Egyras/HeishaMon/HeishaMon/src/opentherm/opentherm.cpp

/*
  OpenTherm.cpp - OpenTherm Communication Library For Arduino, ESP8266
  Copyright 2018, Ihor Melnyk
*/

#include "opentherm.h"

OpenTherm::OpenTherm(int inPin, int outPin, bool isSlave)
  : status(OpenThermStatus::NOT_INITIALIZED),
    inPin(inPin),
    outPin(outPin),
    isSlave(isSlave),
    response(0),
    responseStatus(OpenThermResponseStatus::NONE),
    responseTimestamp(0),
    handleInterruptCallback(NULL),
    processResponseCallback(NULL) {
}

void OpenTherm::begin(void (*handleInterruptCallback)(void), void (*processResponseCallback)(unsigned long, OpenThermResponseStatus)) {
  pinMode(inPin, INPUT);
  pinMode(outPin, OUTPUT);
  if (handleInterruptCallback != NULL) {
    this->handleInterruptCallback = handleInterruptCallback;
    attachInterrupt(digitalPinToInterrupt(inPin), handleInterruptCallback, CHANGE);
  }
  activateBoiler();
  status = OpenThermStatus::READY;
  this->processResponseCallback = processResponseCallback;
}

void OpenTherm::begin(void (*handleInterruptCallback)(void)) {
  begin(handleInterruptCallback, NULL);
}

bool IRAM_ATTR OpenTherm::isReady() {
  return status == OpenThermStatus::READY;
}

int IRAM_ATTR OpenTherm::readState() {
  return digitalRead(inPin);
}

void OpenTherm::setActiveState() {
  digitalWrite(outPin, !logicalSendHigh);
}

void OpenTherm::setIdleState() {
  digitalWrite(outPin, logicalSendHigh);
}

void OpenTherm::activateBoiler() {
  setIdleState();
  delay(1000);
}

void OpenTherm::sendBit(bool high) {
  if (high) setActiveState();
  else setIdleState();
  delayMicroseconds(500);
  if (high) setIdleState();
  else setActiveState();
  delayMicroseconds(500);
}

bool OpenTherm::sendRequestAync(unsigned long request) {
  //Serial.println("Request: " + String(request, HEX));
  noInterrupts();
  const bool ready = isReady();
  interrupts();

  if (!ready)
    return false;

  status = OpenThermStatus::REQUEST_SENDING;
  response = 0;
  responseStatus = OpenThermResponseStatus::NONE;

  sendBit(HIGH);  //start bit
  for (int i = 31; i >= 0; i--) {
    sendBit(bitRead(request, i));
  }
  sendBit(HIGH);  //stop bit
  setIdleState();

  status = OpenThermStatus::RECEIVE_WAITING;
  responseTimestamp = micros();
  return true;
}

unsigned long OpenTherm::sendRequest(unsigned long request) {
  if (!sendRequestAync(request)) return 0;
  while (!isReady()) {
    process();
    yield();
  }
  return response;
}

bool OpenTherm::sendResponse(unsigned long request) {
  status = OpenThermStatus::REQUEST_SENDING;
  response = 0;
  responseStatus = OpenThermResponseStatus::NONE;

  sendBit(HIGH);  //start bit
  for (int i = 31; i >= 0; i--) {
    sendBit(bitRead(request, i));
  }
  sendBit(HIGH);  //stop bit
  setIdleState();
  status = OpenThermStatus::READY;
  return true;
}

OpenThermResponseStatus OpenTherm::getLastResponseStatus() {
  return responseStatus;
}

void IRAM_ATTR OpenTherm::handleInterrupt() {
  unsigned long newTs = micros();

  if (isSlave && smartPowerEnabled) {
    if ((status == OpenThermStatus::READY) && (smartPowerState == HIGH_POWER) && ((newTs - responseTimestamp) > 9000) && ((newTs - responseTimestamp) < 11000)) {
      //previous transit was from LOW to MEDIUM (via HIGH)
      logicalReceiveHigh = !logicalReceiveHigh;
      status = OpenThermStatus::READY;
      smartPowerState = MEDIUM_POWER;
      return;
    }
    if ((status == OpenThermStatus::RECEIVE_START_BIT) && (smartPowerState == MEDIUM_POWER) && ((newTs - responseTimestamp) > 15000)) {
      //this is a MEDIUM to LOW request
      logicalSendHigh = !logicalSendHigh;
      setIdleState();
      status = OpenThermStatus::READY;
      smartPowerState = LOW_POWER;
      return;
    }
  }

  if (isReady()) {
    if (isSlave && readState() == logicalReceiveHigh) {
      status = OpenThermStatus::RECEIVE_WAITING;
    } else {
      return;
    }
  }


  if (status == OpenThermStatus::RECEIVE_WAITING) {
    if (readState() == logicalReceiveHigh) {
      status = OpenThermStatus::RECEIVE_START_BIT;
      responseTimestamp = newTs;
    } else {
      status = OpenThermStatus::RECEIVE_INVALID;
      responseTimestamp = newTs;
    }
  } else if (status == OpenThermStatus::RECEIVE_START_BIT) {
    if ((newTs - responseTimestamp < 750) && readState() == !logicalReceiveHigh) {
      status = OpenThermStatus::RECEIVE_DATA;
      responseTimestamp = newTs;
      responseBitIndex = 0;
    } else {
      status = OpenThermStatus::RECEIVE_INVALID;
      responseTimestamp = newTs;
    }
  } else if (status == OpenThermStatus::RECEIVE_DATA) {
    if ((newTs - responseTimestamp) > 750) {
      if (responseBitIndex < 32) {
        response = (response << 1) | !(readState() == logicalReceiveHigh);
        responseTimestamp = newTs;
        responseBitIndex++;
      } else {  //stop bit
        status = OpenThermStatus::RECEIVE_READY;
        responseTimestamp = newTs;
      }
    }
  }
}

void OpenTherm::process() {
  noInterrupts();
  OpenThermStatus st = status;
  unsigned long ts = responseTimestamp;
  interrupts();

  unsigned long newTs = micros();

  if (st == OpenThermStatus::RECEIVE_START_BIT && (readState() == LOW) && ((newTs - ts) > 5000000)) {  //short circuit detected, act as on/off
    //Serial.println("Short circuit, switch to on/off");
    status = OpenThermStatus::ON_OFF;
    return;
  } else if (st == OpenThermStatus::ON_OFF) {
    if (readState() == HIGH) {
      //Serial.println("Short circuit removed, switch to opentherm");
      status = OpenThermStatus::NOT_INITIALIZED;
      return;
    } else {
      //Serial.println("Still in on/off, short circuit active.");
      return;
    }
  }

  if (isSlave && smartPowerEnabled && smartPowerState != LOW_POWER && (newTs - ts) > 1150000) {  //timeout for 1 + 15% second. thermostat disconnected? disable smartpower
    logicalReceiveHigh = HIGH;
    logicalSendHigh = HIGH;
    setIdleState();
    smartPowerState = LOW_POWER;
    smartPowerEnabled = false;
    OpenThermStatus::NOT_INITIALIZED;
  }

  if (st == OpenThermStatus::READY) return;

  if (st != OpenThermStatus::NOT_INITIALIZED && (newTs - ts) > 1000000) {
    status = OpenThermStatus::READY;
    responseStatus = OpenThermResponseStatus::TIMEOUT;
    if (processResponseCallback != NULL) {
      processResponseCallback(response, responseStatus);
    }
  } else if (st == OpenThermStatus::RECEIVE_INVALID) {
    status = OpenThermStatus::DELAY;
    responseStatus = OpenThermResponseStatus::INVALID;
    if (processResponseCallback != NULL) {
      processResponseCallback(response, responseStatus);
    }
  } else if (st == OpenThermStatus::RECEIVE_READY) {
    status = OpenThermStatus::DELAY;
    responseStatus = (isSlave ? isValidRequest(response) : isValidResponse(response)) ? OpenThermResponseStatus::SUCCESS : OpenThermResponseStatus::INVALID;
    if (processResponseCallback != NULL) {
      processResponseCallback(response, responseStatus);
    }
  } else if (st == OpenThermStatus::DELAY) {
    if ((newTs - ts) > 100000) {
      status = OpenThermStatus::READY;
    }
  } else if (isSlave && smartPowerEnabled && (st == OpenThermStatus::RECEIVE_START_BIT) && ((newTs - ts) > 5000)) {
    if (smartPowerState == LOW_POWER) {  // currently in normal mode
      logicalSendHigh = !logicalSendHigh;
      logicalReceiveHigh = !logicalReceiveHigh;
      setIdleState();
      status = OpenThermStatus::READY;
      smartPowerState = HIGH_POWER;
    } else if (smartPowerState == HIGH_POWER) {  //switch from HIGH to LOW
      logicalReceiveHigh = !logicalReceiveHigh;
      logicalSendHigh = !logicalSendHigh;
      setIdleState();
      status = OpenThermStatus::READY;
      smartPowerState = LOW_POWER;
    }
  }
}

bool OpenTherm::parity(unsigned long frame)  //odd parity
{
  byte p = 0;
  while (frame > 0) {
    if (frame & 1) p++;
    frame = frame >> 1;
  }
  return (p & 1);
}

OpenThermMessageType OpenTherm::getMessageType(unsigned long message) {
  OpenThermMessageType msg_type = static_cast<OpenThermMessageType>((message >> 28) & 7);
  return msg_type;
}

OpenThermMessageID OpenTherm::getDataID(unsigned long frame) {
  return (OpenThermMessageID)((frame >> 16) & 0xFF);
}

unsigned long OpenTherm::buildRequest(OpenThermMessageType type, OpenThermMessageID id, unsigned int data) {
  unsigned long request = data;
  if (type == OpenThermMessageType::WRITE_DATA) {
    request |= 1ul << 28;
  }
  request |= ((unsigned long)id) << 16;
  if (parity(request)) request |= (1ul << 31);
  return request;
}

unsigned long OpenTherm::buildResponse(OpenThermMessageType type, OpenThermMessageID id, unsigned int data) {
  unsigned long response = data;
  response |= type << 28;
  response |= ((unsigned long)id) << 16;
  if (parity(response)) response |= (1ul << 31);
  return response;
}

bool OpenTherm::isValidResponse(unsigned long response) {
  if (parity(response)) return false;
  byte msgType = (response << 1) >> 29;
  return msgType == READ_ACK || msgType == WRITE_ACK;
}

bool OpenTherm::isValidRequest(unsigned long request) {
  if (parity(request)) return false;
  byte msgType = (request << 1) >> 29;
  return msgType == READ_DATA || msgType == WRITE_DATA;
}

void OpenTherm::end() {
  if (this->handleInterruptCallback != NULL) {
    detachInterrupt(digitalPinToInterrupt(inPin));
  }
}
/*
const char *OpenTherm::statusToString(OpenThermResponseStatus status) {
  switch (status) {
    case NONE: return "NONE";
    case SUCCESS: return "SUCCESS";
    case INVALID: return "INVALID";
    case TIMEOUT: return "TIMEOUT";
    default: return "UNKNOWN";
  }
}

const char *OpenTherm::messageTypeToString(OpenThermMessageType message_type) {
  switch (message_type) {
    case READ_DATA: return "READ_DATA";
    case WRITE_DATA: return "WRITE_DATA";
    case INVALID_DATA: return "INVALID_DATA";
    case RESERVED: return "RESERVED";
    case READ_ACK: return "READ_ACK";
    case WRITE_ACK: return "WRITE_ACK";
    case DATA_INVALID: return "DATA_INVALID";
    case UNKNOWN_DATA_ID: return "UNKNOWN_DATA_ID";
    default: return "UNKNOWN";
  }
}
*/

//building requests

unsigned long OpenTherm::buildSetBoilerStatusRequest(bool enableCentralHeating, bool enableHotWater, bool enableCooling, bool enableOutsideTemperatureCompensation, bool enableCentralHeating2) {
  unsigned int data = enableCentralHeating | (enableHotWater << 1) | (enableCooling << 2) | (enableOutsideTemperatureCompensation << 3) | (enableCentralHeating2 << 4);
  data <<= 8;
  return buildRequest(OpenThermMessageType::READ_DATA, OpenThermMessageID::Status, data);
}

unsigned long OpenTherm::buildSetBoilerTemperatureRequest(float temperature) {
  unsigned int data = temperatureToData(temperature);
  return buildRequest(OpenThermMessageType::WRITE_DATA, OpenThermMessageID::TSet, data);
}

unsigned long OpenTherm::buildGetBoilerTemperatureRequest() {
  return buildRequest(OpenThermMessageType::READ_DATA, OpenThermMessageID::Tboiler, 0);
}

//parsing responses
bool OpenTherm::isFault(unsigned long response) {
  return response & 0x1;
}

bool OpenTherm::isCentralHeatingActive(unsigned long response) {
  return response & 0x2;
}

bool OpenTherm::isHotWaterActive(unsigned long response) {
  return response & 0x4;
}

bool OpenTherm::isFlameOn(unsigned long response) {
  return response & 0x8;
}

bool OpenTherm::isCoolingActive(unsigned long response) {
  return response & 0x10;
}

bool OpenTherm::isDiagnostic(unsigned long response) {
  return response & 0x40;
}

uint16_t OpenTherm::getUInt(const unsigned long response) const {
  const uint16_t u88 = response & 0xffff;
  return u88;
}

float OpenTherm::getFloat(const unsigned long response) const {
  const uint16_t u88 = getUInt(response);
  const float f = (u88 & 0x8000) ? -(0x10000L - u88) / 256.0f : u88 / 256.0f;
  return f;
}

unsigned int OpenTherm::temperatureToData(float temperature) {
  if (temperature < 0) temperature = 0;
  if (temperature > 100) temperature = 100;
  unsigned int data = (unsigned int)(temperature * 256);
  return data;
}

//basic requests

unsigned long OpenTherm::setBoilerStatus(bool enableCentralHeating, bool enableHotWater, bool enableCooling, bool enableOutsideTemperatureCompensation, bool enableCentralHeating2) {
  return sendRequest(buildSetBoilerStatusRequest(enableCentralHeating, enableHotWater, enableCooling, enableOutsideTemperatureCompensation, enableCentralHeating2));
}

bool OpenTherm::setBoilerTemperature(float temperature) {
  unsigned long response = sendRequest(buildSetBoilerTemperatureRequest(temperature));
  return isValidResponse(response);
}

float OpenTherm::getBoilerTemperature() {
  unsigned long response = sendRequest(buildGetBoilerTemperatureRequest());
  return isValidResponse(response) ? getFloat(response) : 0;
}

float OpenTherm::getReturnTemperature() {
  unsigned long response = sendRequest(buildRequest(OpenThermRequestType::READ, OpenThermMessageID::Tret, 0));
  return isValidResponse(response) ? getFloat(response) : 0;
}

bool OpenTherm::setDHWSetpoint(float temperature) {
  unsigned int data = temperatureToData(temperature);
  unsigned long response = sendRequest(buildRequest(OpenThermMessageType::WRITE_DATA, OpenThermMessageID::TdhwSet, data));
  return isValidResponse(response);
}

float OpenTherm::getDHWTemperature() {
  unsigned long response = sendRequest(buildRequest(OpenThermMessageType::READ_DATA, OpenThermMessageID::Tdhw, 0));
  return isValidResponse(response) ? getFloat(response) : 0;
}

float OpenTherm::getModulation() {
  unsigned long response = sendRequest(buildRequest(OpenThermRequestType::READ, OpenThermMessageID::RelModLevel, 0));
  return isValidResponse(response) ? getFloat(response) : 0;
}

float OpenTherm::getPressure() {
  unsigned long response = sendRequest(buildRequest(OpenThermRequestType::READ, OpenThermMessageID::CHPressure, 0));
  return isValidResponse(response) ? getFloat(response) : 0;
}

unsigned char OpenTherm::getFault() {
  return ((sendRequest(buildRequest(OpenThermRequestType::READ, OpenThermMessageID::ASFflags, 0)) >> 8) & 0xff);
}

void OpenTherm::setSmartPower(bool state) {
  smartPowerEnabled = state;
  smartPowerState = LOW_POWER;  //check later if this is the right location, maybe in begin
}
