Egyras/HeishaMon/HeishaMon/commands.h

#define LWIP_INTERNAL

#include <ArduinoJson.h>

#define DATASIZE 203

#define INITIALQUERYSIZE 7
extern byte initialQuery[INITIALQUERYSIZE];
#define PANASONICQUERYSIZE 110
extern byte panasonicQuery[PANASONICQUERYSIZE];


#define OPTDATASIZE 20
#define OPTIONALPCBQUERYTIME 1000 //send optional pcb query each second
#define OPTIONALPCBQUERYSIZE 19
#define OPTIONALPCBSAVETIME 300 //save each 5 minutes the current optional pcb state into flash to have valid values during reboot
extern byte optionalPCBQuery[OPTIONALPCBQUERYSIZE];


extern const char* mqtt_topic_values;
extern const char* mqtt_topic_xvalues;
extern const char* mqtt_topic_commands;
extern const char* mqtt_topic_pcbvalues;
extern const char* mqtt_topic_1wire;
extern const char* mqtt_topic_s0;
extern const char* mqtt_topic_pcb;
extern const char* mqtt_logtopic;
extern const char* mqtt_willtopic;
extern const char* mqtt_iptopic;
extern const char* mqtt_send_raw_value_topic;

unsigned int set_heatpump_state(char *msg, unsigned char *cmd, char *log_msg);
unsigned int set_pump(char *msg, unsigned char *cmd, char *log_msg);
unsigned int set_max_pump_duty(char *msg, unsigned char *cmd, char *log_msg);
unsigned int set_quiet_mode(char *msg, unsigned char *cmd, char *log_msg);
unsigned int set_z1_heat_request_temperature(char *msg, unsigned char *cmd, char *log_msg);
unsigned int set_z1_cool_request_temperature(char *msg, unsigned char *cmd, char *log_msg);
unsigned int set_z2_heat_request_temperature(char *msg, unsigned char *cmd, char *log_msg);
unsigned int set_z2_cool_request_temperature(char *msg, unsigned char *cmd, char *log_msg);
unsigned int set_force_DHW(char *msg, unsigned char *cmd, char *log_msg);
unsigned int set_force_defrost(char *msg, unsigned char *cmd, char *log_msg);
unsigned int set_force_sterilization(char *msg, unsigned char *cmd, char *log_msg);
unsigned int set_holiday_mode(char *msg, unsigned char *cmd, char *log_msg);
unsigned int set_powerful_mode(char *msg, unsigned char *cmd, char *log_msg);
unsigned int set_operation_mode(char *msg, unsigned char *cmd, char *log_msg);
unsigned int set_DHW_temp(char *msg, unsigned char *cmd, char *log_msg);
unsigned int set_curves(char *msg, unsigned char *cmd, char *log_msg);
unsigned int set_zones(char *msg, unsigned char *cmd, char *log_msg);
unsigned int set_floor_heat_delta(char *msg, unsigned char *cmd, char *log_msg);
unsigned int set_floor_cool_delta(char *msg, unsigned char *cmd, char *log_msg);
unsigned int set_dhw_heat_delta(char *msg, unsigned char *cmd, char *log_msg);
unsigned int set_reset(char *msg, unsigned char *cmd, char *log_msg);
unsigned int set_heater_delay_time(char *msg, unsigned char *cmd, char *log_msg);
unsigned int set_heater_start_delta(char *msg, unsigned char *cmd, char *log_msg);
unsigned int set_heater_stop_delta(char *msg, unsigned char *cmd, char *log_msg);
unsigned int set_main_schedule(char *msg, unsigned char *cmd, char *log_msg);
unsigned int set_alt_external_sensor(char *msg, unsigned char *cmd, char *log_msg);
unsigned int set_external_pad_heater(char *msg, unsigned char *cmd, char *log_msg);
unsigned int set_buffer_delta(char *msg, unsigned char *cmd, char *log_msg);
unsigned int set_buffer(char *msg, unsigned char *cmd, char *log_msg);
unsigned int set_heatingoffoutdoortemp(char *msg, unsigned char *cmd, char *log_msg);
unsigned int set_bivalent_control(char *msg, unsigned char *cmd, char *log_msg);
unsigned int set_bivalent_mode(char *msg, unsigned char *cmd, char *log_msg);
unsigned int set_bivalent_start_temp(char *msg, unsigned char *cmd, char *log_msg);
unsigned int set_bivalent_ap_start_temp(char *msg, unsigned char *cmd, char *log_msg);
unsigned int set_bivalent_ap_stop_temp(char *msg, unsigned char *cmd, char *log_msg);
unsigned int set_external_control(char *msg, unsigned char *cmd, char *log_msg);
unsigned int set_external_error(char *msg, unsigned char *cmd, char *log_msg);
unsigned int set_heatingcontrol(char *msg, unsigned char *cmd, char *log_msg);
unsigned int set_smart_dhw(char *msg, unsigned char *cmd, char *log_msg);
unsigned int set_quiet_mode_priority(char *msg, unsigned char *cmd, char *log_msg);
unsigned int set_pump_flowrate_mode(char *msg, unsigned char *cmd, char *log_msg);


//optional pcb commands
unsigned int set_heat_cool_mode(char *msg, char *log_msg);
unsigned int set_compressor_state(char *msg, char *log_msg);
unsigned int set_smart_grid_mode(char *msg, char *log_msg);
unsigned int set_external_thermostat_1_state(char *msg, char *log_msg);
unsigned int set_external_thermostat_2_state(char *msg, char *log_msg);
unsigned int set_demand_control(char *msg, char *log_msg);
unsigned int set_pool_temp(char *msg, char *log_msg);
unsigned int set_buffer_temp(char *msg, char *log_msg);
unsigned int set_z1_room_temp(char *msg, char *log_msg);
unsigned int set_z1_water_temp(char *msg, char *log_msg);
unsigned int set_z2_room_temp(char *msg, char *log_msg);
unsigned int set_z2_water_temp(char *msg, char *log_msg);
unsigned int set_solar_temp(char *msg, char *log_msg);
unsigned int set_byte_9(char *msg, char *log_msg);
unsigned int set_external_compressor_control(char *msg, unsigned char *cmd, char *log_msg);
unsigned int set_external_heat_cool_control(char *msg, unsigned char *cmd, char *log_msg);

struct cmdStruct {
  char name[29];
  unsigned int (*func)(char *msg, unsigned char *cmd, char *log_msg);
};

const cmdStruct commands[] PROGMEM = {
  // set heatpump state to on by sending 1
  { "SetHeatpump", set_heatpump_state },
  // set pump state to on by sending 1
  { "SetPump", set_pump },
  // set max pump duty
  { "SetMaxPumpDuty", set_max_pump_duty },
  // set 0 for Off mode, set 1 for Quiet mode 1, set 2 for Quiet mode 2, set 3 for Quiet mode 3
  { "SetQuietMode", set_quiet_mode },
  // z1 heat request temp -  set from -5 to 5 to get same temperature shift point or set direct temp
  { "SetZ1HeatRequestTemperature", set_z1_heat_request_temperature },
  // z1 cool request temp -  set from -5 to 5 to get same temperature shift point or set direct temp
  { "SetZ1CoolRequestTemperature", set_z1_cool_request_temperature },
  // z2 heat request temp -  set from -5 to 5 to get same temperature shift point or set direct temp
  { "SetZ2HeatRequestTemperature", set_z2_heat_request_temperature },
  // z2 cool request temp -  set from -5 to 5 to get same temperature shift point or set direct temp
  { "SetZ2CoolRequestTemperature", set_z2_cool_request_temperature },
  // set mode to force DHW by sending 1
  { "SetForceDHW", set_force_DHW },
  // set mode to force defrost  by sending 1
  { "SetForceDefrost", set_force_defrost },
  // set mode to force sterilization by sending 1
  { "SetForceSterilization", set_force_sterilization },
  // set Holiday mode by sending 1, off will be 0
  { "SetHolidayMode", set_holiday_mode },
  // set Powerful mode by sending 0 = off, 1 for 30min, 2 for 60min, 3 for 90 min
  { "SetPowerfulMode", set_powerful_mode },
  // set Heat pump operation mode  3 = DHW only, 0 = heat only, 1 = cool only, 2 = Auto, 4 = Heat+DHW, 5 = Cool+DHW, 6 = Auto + DHW
  { "SetOperationMode", set_operation_mode },
  // set DHW temperature by sending desired temperature between 40C-75C
  { "SetDHWTemp", set_DHW_temp },
  // set heat/cool curves on z1 and z2 using a json input
  { "SetCurves", set_curves },
  // set zones to active
  { "SetZones", set_zones },
  { "SetFloorHeatDelta", set_floor_heat_delta },
  { "SetFloorCoolDelta", set_floor_cool_delta },
  { "SetDHWHeatDelta", set_dhw_heat_delta },
  { "SetReset", set_reset },
  { "SetHeaterDelayTime", set_heater_delay_time },
  { "SetHeaterStartDelta", set_heater_start_delta },
  { "SetHeaterStopDelta", set_heater_stop_delta },
  { "SetMainSchedule", set_main_schedule },
  { "SetAltExternalSensor", set_alt_external_sensor },
  { "SetExternalPadHeater", set_external_pad_heater },
  { "SetBufferDelta", set_buffer_delta },
  { "SetBuffer", set_buffer },
  // set Outdoor Temperature to stop heating 5-35
  { "SetHeatingOffOutdoorTemp", set_heatingoffoutdoortemp },
  { "SetExternalControl", set_external_control },
  { "SetExternalError", set_external_error },
  { "SetExternalCompressorControl", set_external_compressor_control },
  { "SetExternalHeatCoolControl", set_external_heat_cool_control },
  // set Bivalent control mode  0 = off, 1 = on
  { "SetBivalentControl", set_bivalent_control },
  // set Bivalent operation mode  0 = Alternativ, 1 = Parallel, 2 = Advanced Parallel
  { "SetBivalentMode", set_bivalent_mode },
  // bivalent start temp -  set from -15C to 35C 
  { "SetBivalentStartTemp", set_bivalent_start_temp },
  // bivalent AP start temp -  set from -15C to 35C 
  { "SetBivalentAPStartTemp", set_bivalent_ap_start_temp },
  // bivalent AP stop temp -  set from -15C to 35C
  { "SetBivalentAPStopTemp", set_bivalent_ap_stop_temp },
  { "SetHeatingControl", set_heatingcontrol },
  { "SetSmartDHW", set_smart_dhw },
  { "SetQuietModePriority", set_quiet_mode_priority },
  { "SetPumpFlowrateMode", set_pump_flowrate_mode },
};

struct optCmdStruct{
  char name[28];
  unsigned int (*func)(char *msg, char *log_msg);
};

const optCmdStruct optionalCommands[] PROGMEM = {
  // optional PCB
  { "SetHeatCoolMode", set_heat_cool_mode },
  { "SetCompressorState", set_compressor_state },
  { "SetSmartGridMode", set_smart_grid_mode },
  { "SetExternalThermostat1State", set_external_thermostat_1_state },
  { "SetExternalThermostat2State", set_external_thermostat_2_state },
  { "SetDemandControl", set_demand_control },
  { "SetPoolTemp", set_pool_temp },
  { "SetBufferTemp", set_buffer_temp },
  { "SetZ1RoomTemp", set_z1_room_temp },
  { "SetZ1WaterTemp", set_z1_water_temp },
  { "SetZ2RoomTemp", set_z2_room_temp },
  { "SetZ2WaterTemp", set_z2_water_temp },
  { "SetSolarTemp", set_solar_temp },
  { "SetOptPCBByte9", set_byte_9 }
};

void send_heatpump_command(char* topic, char *msg, bool (*send_command)(byte*, int), void (*log_message)(char*), bool optionalPCB);
bool saveOptionalPCB(byte* command, int length);
bool loadOptionalPCB(byte* command, int length);
