Egyras/HeishaMon/HeishaMon/decode.cpp

#include "decode.h"
#include "commands.h"
#include "rules.h"
#include "src/common/progmem.h"

void websocket_write_all(char *data, uint16_t data_len);

unsigned long lastalldatatime = 0;
unsigned long lastallextradatatime = 0;
unsigned long lastalloptdatatime = 0;

String getBit1(byte input) {
  return String(input  >> 7);
}

String getBit1and2(byte input) {
  return String((input  >> 6) - 1);
}

String getBit3and4(byte input) {
  return String(((input >> 4) & 0b11) - 1);
}

String getBit5and6(byte input) {
  return String(((input >> 2) & 0b11) - 1);
}

String getBit7and8(byte input) {
  return String((input & 0b11) - 1);
}

String getBit3and4and5(byte input) {
  return String(((input >> 3) & 0b111) - 1);
}

String getLeft5bits(byte input) {
  return String((input >> 3) - 1);
}

String getRight3bits(byte input) {
  return String((input & 0b111) - 1);
}

String getIntMinus1(byte input) {
  int value = (int)input - 1;
  return (String)value;
}

String getIntMinus128(byte input) {
  int value = (int)input - 128;
  return (String)value;
}

String getIntMinus1Div5(byte input) {
  return String((((float)input - 1) / 5), 1);
}

String getIntMinus1Div50(byte input) {
  return String((((float)input - 1) / 50), 2);
}

String getIntMinus1Times10(byte input) {
  int value = (int)input - 1;
  return (String)(value * 10);
}

String getIntMinus1Times50(byte input) {
  int value = (int)input - 1;
  return (String)(value * 50);
}


String unknown(byte input) {
  return "-1";
}

String getValvePID(byte input) {
  return String((((float)input - 1) / 2), 1);
}

String getOpMode(byte input) {
  switch ((int)(input & 0b111111)) {
    case 18:
      return "0";
    case 19:
      return "1";
    case 25:
      return "2";
    case 33:
      return "3";
    case 34:
      return "4";
    case 35:
      return "5";
    case 41:
      return "6";
    case 26:
      return "7";
    case 42:
      return "8";
    default:
      return "-1";
  }
}

String getModel(char* data) { // TOP92 //
  byte model[10] = { data[129], data[130], data[131], data[132], data[133], data[134], data[135], data[136], data[137], data[138]};
  char modelResult[31];
  for (size_t i = 0; i < 10; ++i) {
    sprintf(&modelResult[i*3], "%02X ", model[i]);
  }
  modelResult[29] = '\0';
  return String(modelResult);
}

String getPower(byte input) {
  int value = ((int)input - 1) * 200;
  return (String)value;
}

String getUintt16(char* data, byte addr) {
  uint16_t value = static_cast<uint16_t>((data[addr + 1] << 8) | data[addr]);
  return (String)(value - 1);
}

String getPumpFlow(char* data) {  // TOP1 //
  int PumpFlow1 = (int)data[170];
  float PumpFlow2 = (((float)data[169] - 1) / 256);
  float PumpFlow = PumpFlow1 + PumpFlow2;
  return String(PumpFlow, 2);
}

String getErrorInfo(char* data) { // TOP44 //
  int Error_type = (int)(data[113]);
  int Error_number = ((int)(data[114])) - 17;
  char Error_string[10];
  switch (Error_type) {
    case 177:                  //B1=F type error
      sprintf(Error_string, "F%02X", Error_number);
      break;
    case 161:                  //A1=H type error
      sprintf(Error_string, "H%02X", Error_number);
      break;
    default:
      sprintf(Error_string, "No error");
      break;
  }
  return String(Error_string);
}


void resetlastalldatatime() {
  lastalldatatime = 0;
  lastallextradatatime = 0;
  lastalloptdatatime = 0;
}
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
